Vic-Syryn/EcoLux/reports and protocols/Ecolux_Protocol_Gebruikerstesten_Wave_1.pdf

# EcoLux gebruikerstesten wave 1 protocol

### Projectinformatie

Projectnaam: EcoLux
Dit project onderzoekt hoe slimme, toegankelijke producten mensen kunnen helpen om thuis energie te besparen. De focus ligt op oplossingen die zowel financieel voordeel opleveren voor de gebruiker als milieuwinst genereren. Hierbij ligt de focus om het voor de gebruiker zo makkelijk mogelijk te maken.

Interviewer: Yenthe Bode (yenthe.bode@ugent.be), student Industrieel Ontwerpen aan de Universiteit Gent

### Doelstelling en kadering

In de 1ste wave willen we de customer journey meer in detail bekijken en ons focussen op de functionaliteit zodat we in de 2de wave kunnen focussen op inzoomen op de conclusies van de 1ste wave. We willen bepalen hoe we het energieverlies moeten communiceren, we doen dit aan de hand van gebruikerstest/interview.

### Respondenten

Er werd gekozen om mensen die renoveren de proeven te laten uitvoeren.

De gebruikerstesten duren 1 uur en worden afgenomen van 29 tot 30 november 2025.

Steekproefomschrijving (N = 3)

pseudonym | respondent type | interview date | interview location
Sabine | | 08-12-2025 | Zijn/haar huis
Alain | | 08-12-2025 | Zijn/haar huis
Evelyne | | 10-12-2025 | Zijn/haar huis

### Onderzoeksvragen

Hoe communiceren we het best het energieverlies bij de gebruiker(awareness)?

Hoe zou de gebruiker willen dat het product wordt geinstalleerd?

Wat is voor de gebruiker de belangrijkste feauture waarom de gebruiker het zou kopen?

Is een of meerdere substations noodzakelijk?

### Overzicht van de discussiegids en tijdsinschatting

- Deel 1 – Introductie en voorstelling concept(5’)
- Deel 2 – Voorstelling Interviewer (5’)
- Deel 3 – Testen prototypes en interview (25’)
- Deel 4 – Conclusie (15’)

### Materialen

- De 3 prototypes en de substations
- Gsm voor opnames
- Dit protocol
- Informed consent

### Discussiegids

### Introductie en voorstelling concept (5’)

Bedankt voor je deelname aan dit onderzoek.

Ik zal starten met het project en ons voor te stellen.

Wij zijn Vic Syryn, Viktor Caluwaert en Yenthe Bode en wij studeren aan de universiteit Gent campus Kortrijk met afstudeerrichting industrieel ingenieur industrieel ontwerpen.

Deze gebruikerstest maakt deel uit van ons project Ecolux. De Ecolux is een thuisassistent die helpt de gebruiker energie te besparen. Door overal in je huis slimme technologie te plaatsen, is de EcoLux altijd op de hoogte van waar je energie verbruikt en dus ook waar je er verliest. Bijvoorbeeld: iemand vergeet het licht uit te doen in de badkamer waardoor er energie verloren gaat, de EcoLux laat dit weten aan de gebruiker en lost dit indien gewenst zelf op. Een ander voorbeeld: stel dat je de verwarming aan laat en je raam staat nog open in je slaapkamer, laat de EcoLux dit opnieuw weten en kan je dan zelf kiezen om je raam toe te doen. Finaal heb je nog de huis-verlaat-modus. Wanneer je het huis wil verlaten, zal de EcoLux eerst nagaan of er energie verloren gaat terwijl je weg bent. Hij laat dit dan weten en regelt zelf lichten en sluit sluipverbruikers af...waar nodig.

In deze test willen we vooral kijken welke manier van communiceren van het probleem naar de gebruiker het beste werkt. Ik ben erg benieuwd naar jouw inzichten en ervaringen. Er zijn geen juiste of foute antwoorden/handelingen. Wij zijn gebaat bij jouw oprechte feedback rond de topics die we zullen behandelen.

We willen zeker nog onderstrepen dat alles wat straks in het gesprek aan bod komt in absolute confidentialiteit behandeld wordt. We zijn als studenten aan de Ugent namelijk gebonden aan de Europese privacyrichtlijnen. Voor de synthese met de inzichten en aanbevelingen worden individuele meningen sowieso ook geanonimiseerd. Je naam zal met andere woorden niet gekoppeld worden aan specifieke uitspraken. Een meer gedetailleerde beschrijving van onze intenties, verwerking van gegevens, en algemeen beleid kan je nalezen in de ‘Informed Consent’. Voor we van start kunnen met de gebruikertesten, heb ik jouw expliciet akkoord nodig met dit document.

Ten slotte, vroegen we ons af of we straks dit gesprek mogen opnemen/filmen , om ons gesprek en je handelingen achteraf te kunnen bekijken en analyseren. Uiteraard wordt deze opname niet gedeeld met derden, en verwijderd na afloop van het project. Als u hiermee akkoord gaat, stel ik voordat we het interview beginnen.

[invullen informed consent & start recording]

### Framing questions

Voorstelling Interviewer (5’)

Alvorens we in de materie duiken, wil ik graag eerst even kennismaken.

- Kan je kort iets over jezelf vertellen en met wie je samenwoont?
- Hoe ziet je huishouden eruit (alleen, met partner, gezin, huisgenoten…)?
- Kan je wat vertellen over je woning?
- Woon je in een huis of appartement?

### Testen Prototypes en interview

Voor elk communicatie-prototype wordt het volgende getest:
- Laat de gebruiker passeren voorbij het prototype als er geen energie verlies is en als er wel energieverlies is.
- De gebruiker staat stil en het prototype verandert van geen energieverlies naar wel energie verlies.
- “Huis verlaten/ thuis komen” functie testen.
- Ondertussen vragen stellen over de duidelijkheid van de communicatie.
Welke van de 3 prototypes heeft jouw voorkeur en waarom?

Substation prototypes voorleggen en volgende testen doen:
- Kijken hoe de gebruiker intrageert met de substation op verschillende locaties.
- Indien ze de substations nuttig vinden:
- Welke features hierop nuttig zijn?

Welke features vind jij het belangrijkst voor het product?

Hoe zou je willen dat het product wordt geinstalleerd?

### Wrap-up

Wenst u zelf nog zaken toe te voegen?

De belangrijkste zaken die ik heb geleerd uit deze gebruikerstesten zijn, … Heb ik het juist begrepen als …?
Wat zijn de belangrijkste elementen waarvan u denkt dat ik die het meest zou moeten onthouden?

Hartelijk bedankt voor uw deelname, dit was erg waardevol voor het verdere onderzoek. Wilt u op de hoogte blijven van verdere resultaten of andere gebruikerstesten?

### Data-analyse

De resultaten van dit onderzoek worden opgenomen in een afzonderlijk rapport, waarin
na afloop de videos en audiofragmenten samengevat werden in korte verslagen per respondent. De analyse gebeurde op basis van herhalende patronen in gedrag, attitudes en motivaties. De belangrijkste inzichten werden vervolgens vertaald naar ontwerpimplicaties.
