Vic-Syryn/EcoLux/reports and protocols/Ecolux_Report_Gebruikerstesten_Wave_2 (2).pdf

# EcoLux gebruikerstest wave 2 report

### Projectinformatie

Projectnaam: EcoLux
Dit project onderzoekt hoe slimme, toegankelijke producten mensen kunnen helpen om thuis energie te besparen. De focus ligt op oplossingen die zowel financieel voordeel opleveren voor de gebruiker als milieuwinst genereren. Hierbij ligt de focus om het voor de gebruiker zo makkelijk mogelijk te maken.

Interviewer: Viktor Caluwaert (viktor.caluwaert@ugent.be), student Industrieel Ontwerpen aan de Universiteit Gent

### Doelstelling en kadering

in Wave 1 werd vooral gekeken naar awareness, installatie en basisfunctionaliteit, nu in Wave 2 focussen we op:

- de manier waarop we de informatie het best overbrengen
- de verwachtingen van de gebruiker rond automatisatie vs. manuele controle,
- de rol en het gebruik van een negeerfun

### Onderzoeksvragen

Hoe brengen we de informatie van het energieverlies het best over?

Wat verwacht de gebruiker dat de ecolux automatisch doet en wat er manueel moet gebeuren?, moet dit instelbaar zijn?

Hoe zou de negeerfunctie het best gebruikt worden?

### Methode

Gekozen methode: gebruikerstesten + contextual interview

Motivatie volgens checklist
- We wilden gedrag in context zien → daarom gebruikerstest
- We wilden ook motivaties en voorkeuren achterhalen → aanvullende interviews
- De methode laat ons feedback op prototypes verzamelen voor de functies
- Deze methode is praktijkgericht, snel uitvoerbaar en geschikt voor conceptevaluatie

### Korte versie van het protocol

(Volledig protocol in Ecolux_Protocol_Gebruikerstesten_Wave_2.docx)

- Introductie & informed consent
- Presentatie concept EcoLux
- Testen van 3 prototypes: gebruiker stelt in dat hij/zij de decoder wilt negeren en de rest van de problemen automatisch laat oplossen
- Observatie van gedrag + interviewvragen

Materialen:

- Protype (1)
- Smartphone voor interface
- Smartphone voor opnames
- Informed consent

### Respondenten

Steekproefomschrijving (N = 3)

pseudonym | Respndent type | interview date | interview location
Jan | ingenieur | 20-12-2025 | Zijn/haar huis
Marieke | dokter | 21-12-2025 | Zijn/haar huis
Katrien | Grafisch ontwerper | 20-12-2025 | Zijn/haar huis

Waarom deze doelgroep?

- Uit eerdere fase bleek renoverende huishoudens de sterkste motivatie hebben om te besparen
- Renovaties vormen ideale installatiemomenten
- Verhoogde gevoeligheid voor EPC, energieprijzen en comfort

### Data-analyse

Via spraak:
- Informatie wordt duidelijk gecommuniceerd.
- Als het veel informatie is, is het moeilijk om alles te onthouden en achteraf te kunnnen opnoemen -> alleen dus handig als er weinig energieverliezen zijn
- Duurt lang terwijl sommige dingen je snel weet of gwn direct alles automatisch wilt laten verlopen
Via tekst:
- Makkelijk om snel te scannen
- Makkelijk als je snel wilt handelen
- Niet altijd duidelijk waar met weinig tekst bv de verwarming staat aan en het raam staat op in de slaapkamer van ...
- Ziet er druk uit ( weinig witruimte of weinig informatie geven)
Via grondplan:
- Duidelijk waar het energie verlies is

- Makkelijk en snel handelen
- Voorkeur van de 3 testers

Automatisch:
De gebruiker zou zoveel mogelijk automatisch willen en voor hun hoeft het niet instelbaar zijn.

### Key Insights (Conclusies)

1. Visuele weergave (foto) > tekst/spraak
2. Snelheid is ook belangrijk voor de gebruiker
3. Alles automatiseren

### Implicaties voor het ontwerp (Actionable)

## - EcoLux communiceert energieverliezen via een visuele weergave die de locatie in

de woning duidelijk maakt.

## - EcoLux ondersteunt snelle uitvoering van actie zodra een energieverlies wordt

gedetecteerd.

## - EcoLux automatiseert het oplossen van energieproblemen maximaal, zodat de gebruiker zo weinig mogelijk handelingen hoeft uit te voeren

### Overtuigingskracht van interpretatie

De resultaten zijn consistent over de drie respondenten en vertonen duidelijke voorkeur voor de communicatie via grondplan. De conclusies vloeien logisch voort uit de ruwe data, waardoor de interpretatie betrouwbaar en overtuigend is.
