Vic-Syryn/EcoLux/img/Ecolux_Circuit-1.png

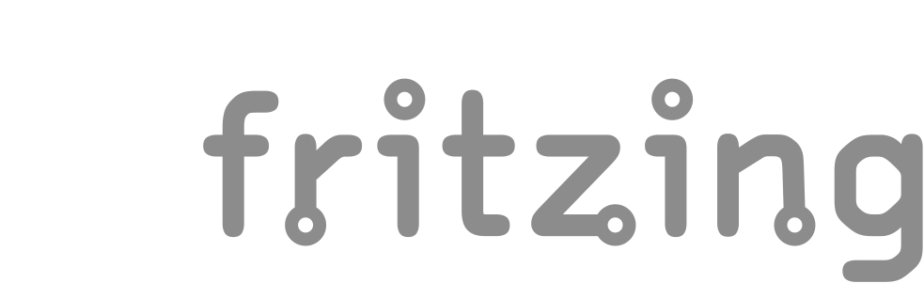
img/Ecolux_Circuit-1.png
