Vic-Syryn/EcoLux/img/Ecolux_Circuit-2.png

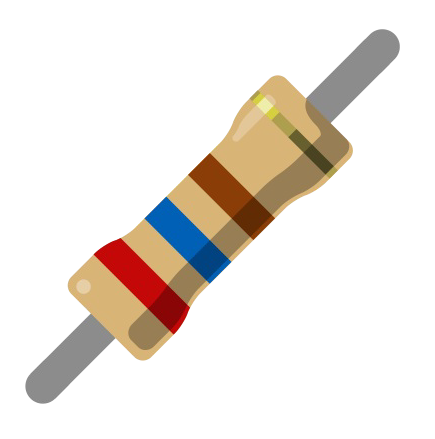
img/Ecolux_Circuit-2.png
