Vic-Syryn/EcoLux/img/Ecolux_Circuit-9.png

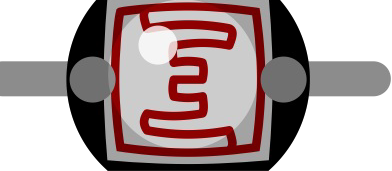
img/Ecolux_Circuit-9.png
