Vic-Syryn/EcoLux/img/Ecolux_Circuit-11.png

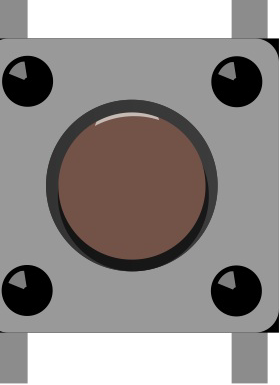
img/Ecolux_Circuit-11.png
