Vic-Syryn/EcoLux/img/methodologie.png

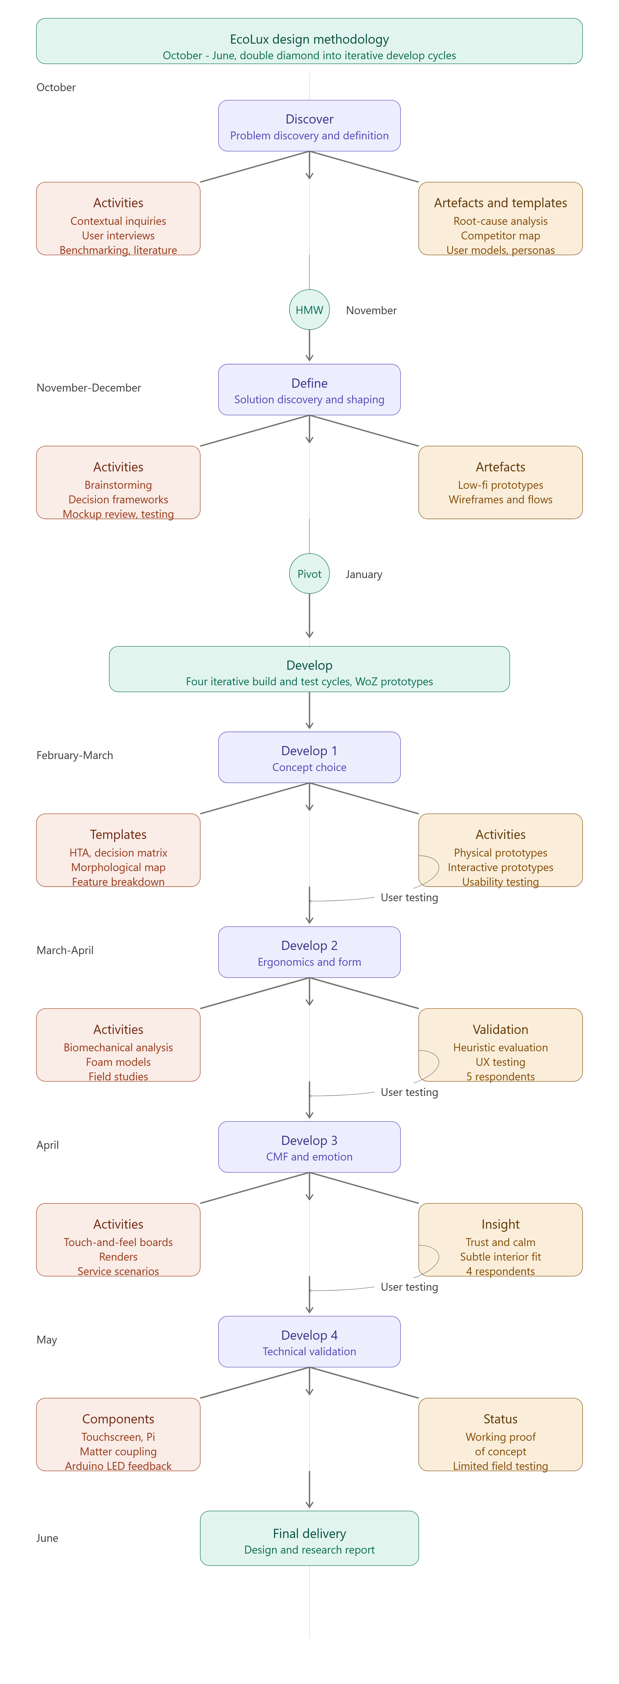
img/methodologie.png
