Vic-Syryn/EcoLux/img/meubel1.png

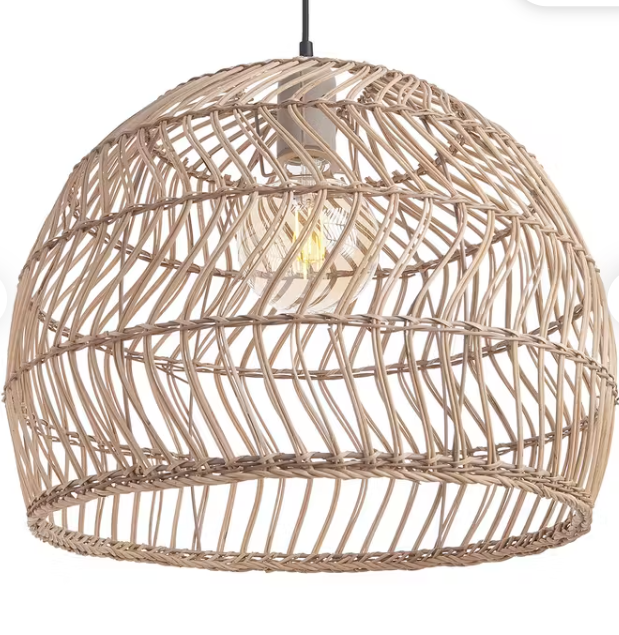
img/meubel1.png
