Vic-Syryn/EcoLux/img/meubel2.png

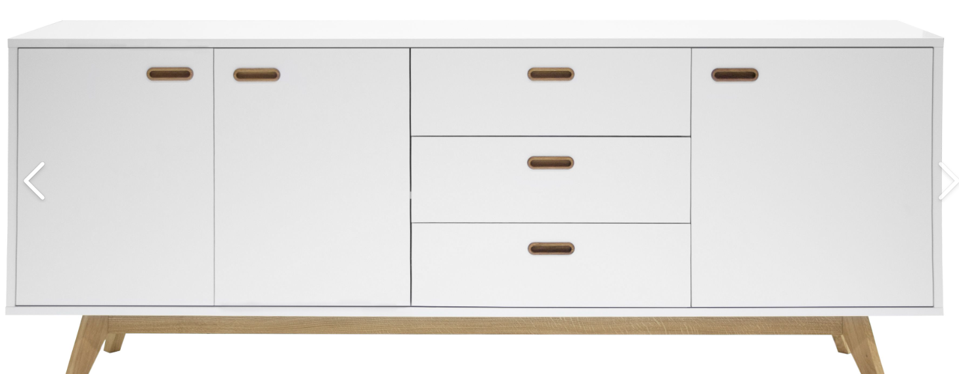
img/meubel2.png
