Vic-Syryn/EcoLux/img/meubel3.png

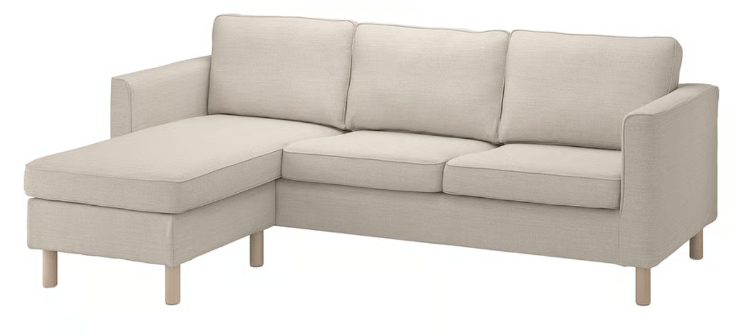
img/meubel3.png
