Vic-Syryn/EcoLux/img/render3.png

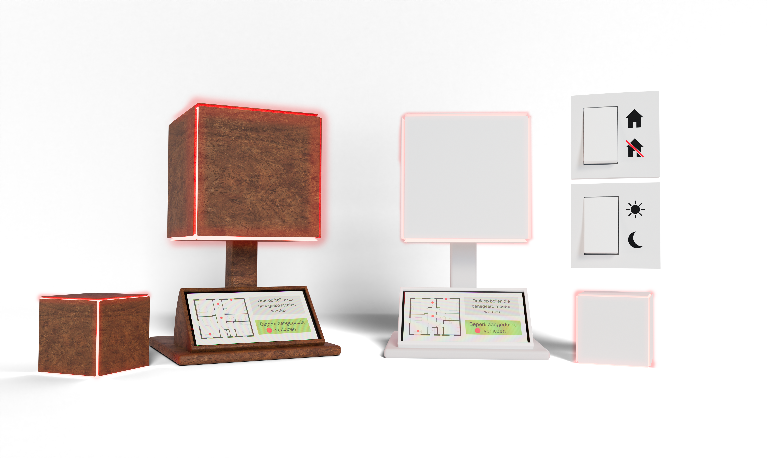
img/render3.png
