Vic-Syryn/EcoLux/img/render12042026.png

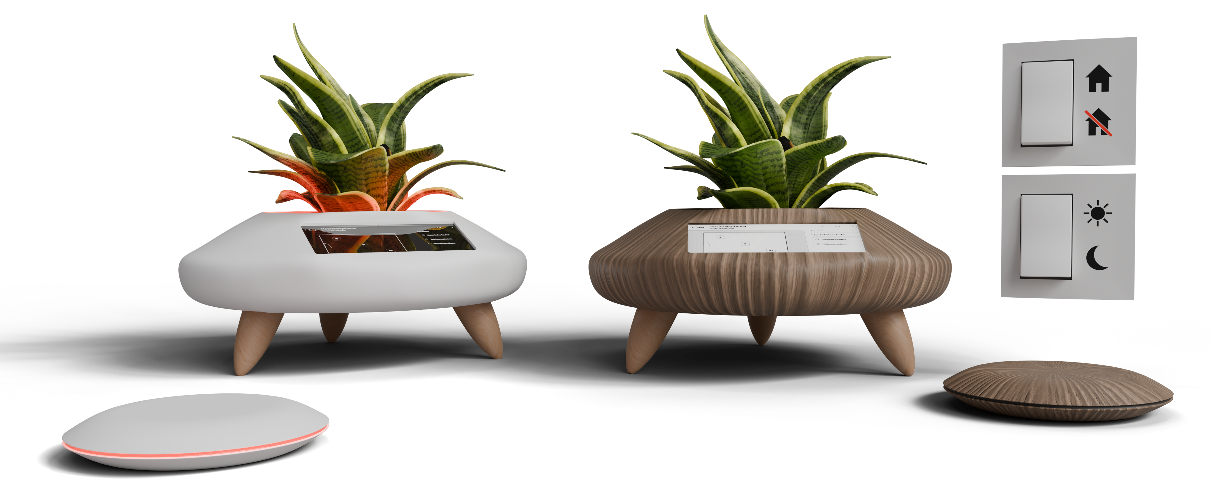
img/render12042026.png
