Vic-Syryn/EcoLux/img/Ecolux_Circuit.pdf

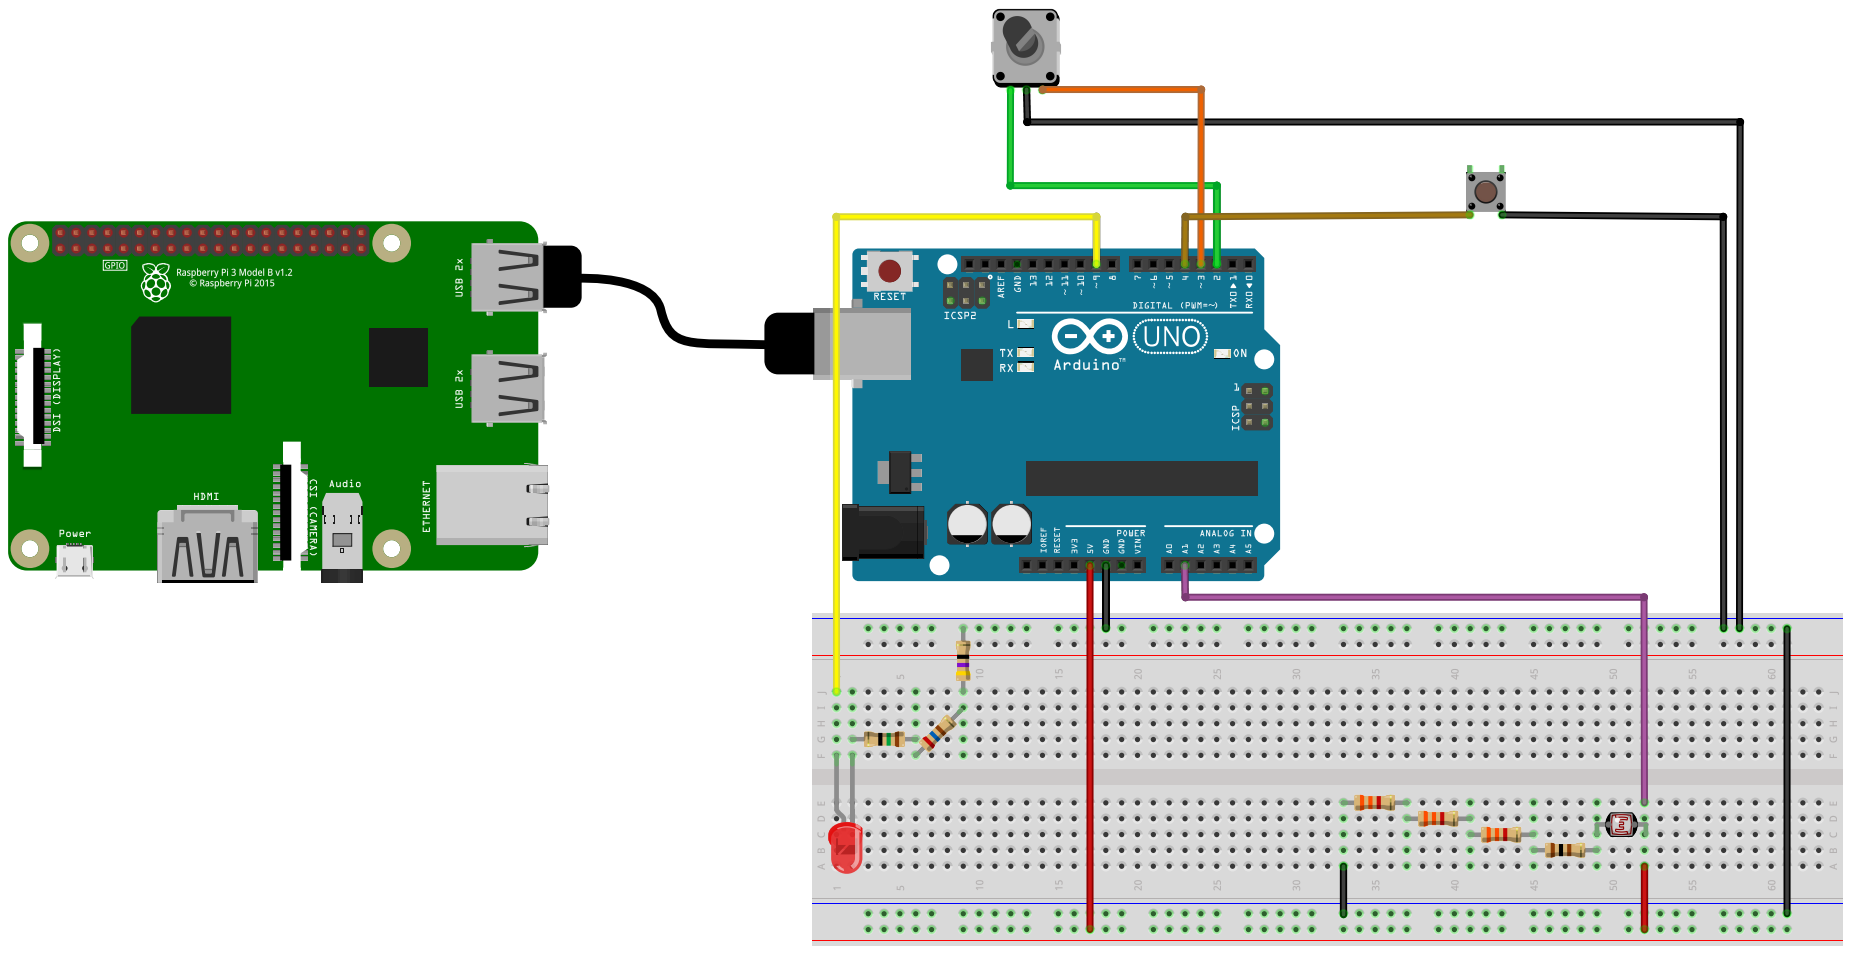
[picture p111: page 1]
